zioCristia/esp-room-thermometer/images/IMG_4551.jpg

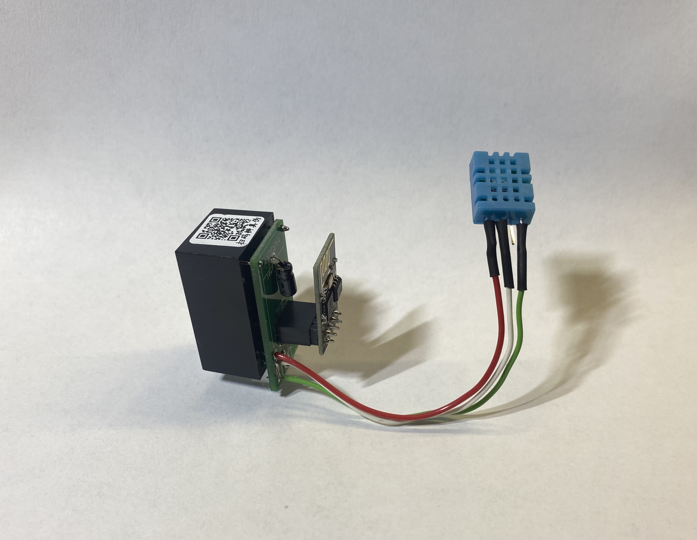
images/IMG_4551.jpg
