zioCristia/esp-room-thermometer/images/IMG_4555.jpg

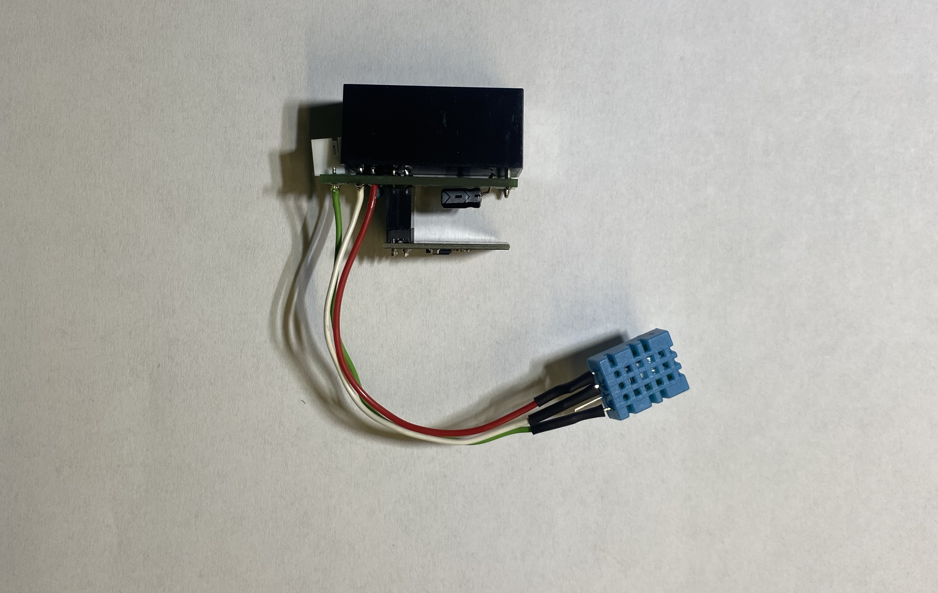
images/IMG_4555.jpg
