zioCristia/esp-room-thermometer/images/IMG_4556.jpg

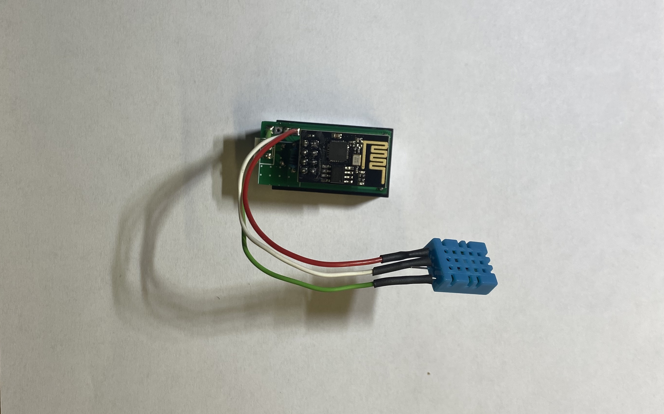
images/IMG_4556.jpg
