zioCristia/esp-room-thermometer/images/IMG_4557.jpg

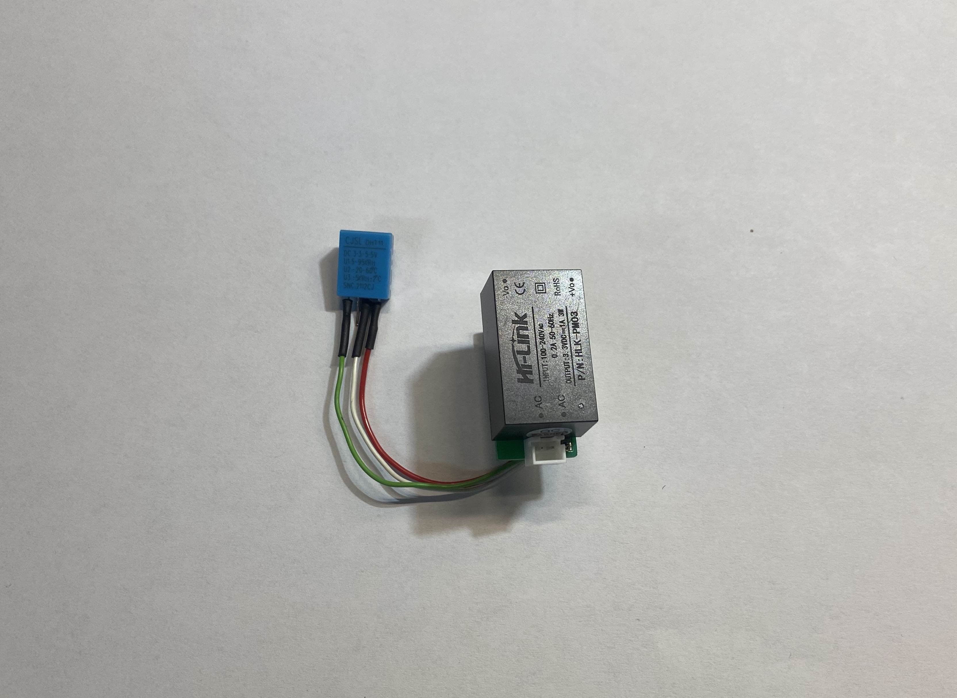
images/IMG_4557.jpg
