zioCristia/esp-room-thermometer/images/IMG_4558.jpg

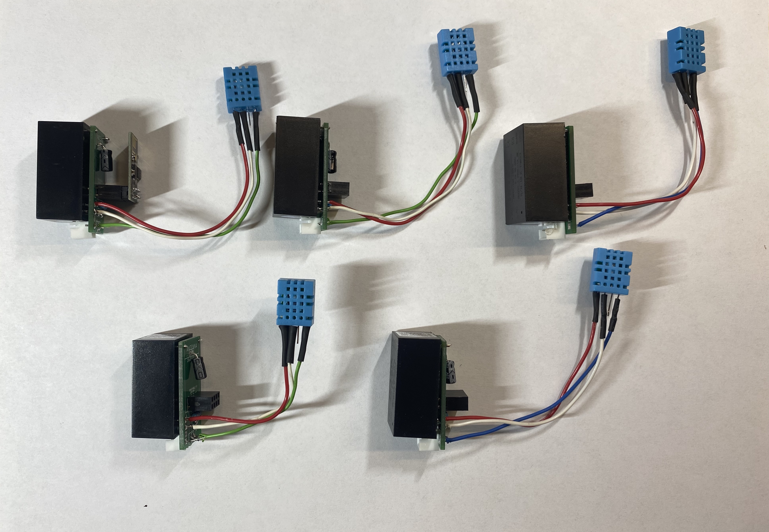
images/IMG_4558.jpg
