zioCristia/esp-room-thermometer/images/IMG_4588.jpg

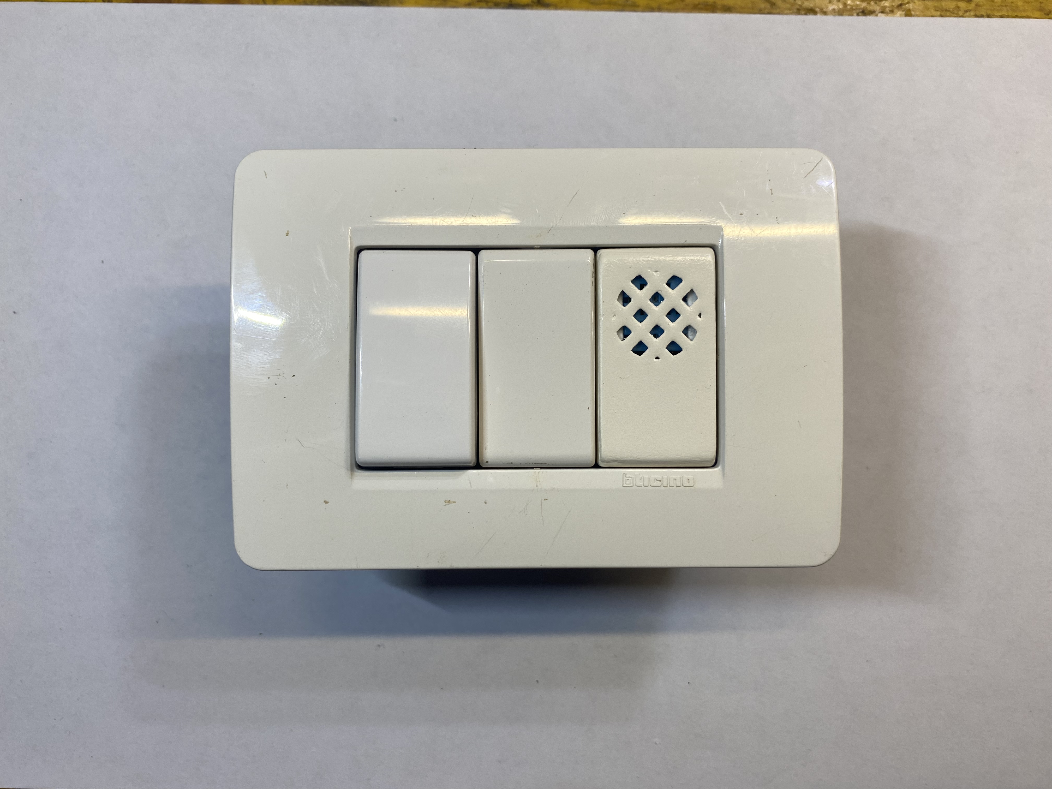
images/IMG_4588.jpg
