zioCristia/esp-room-thermometer/images/IMG_4589.jpg

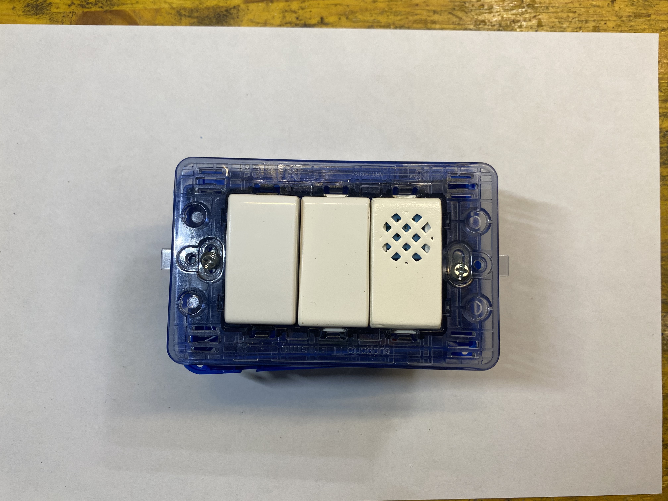
images/IMG_4589.jpg
