zioCristia/esp-room-thermometer/images/IMG_4590.jpg

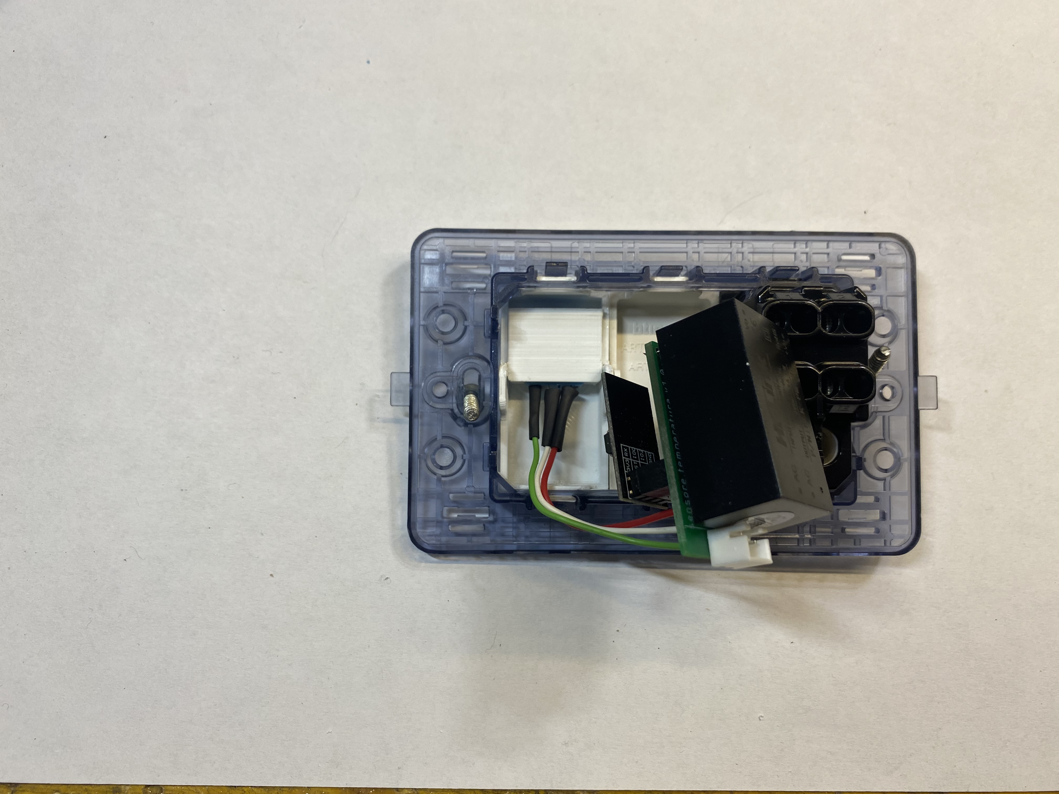
images/IMG_4590.jpg
